Gartenimperator/SWH/resources/First_sketch.jpeg

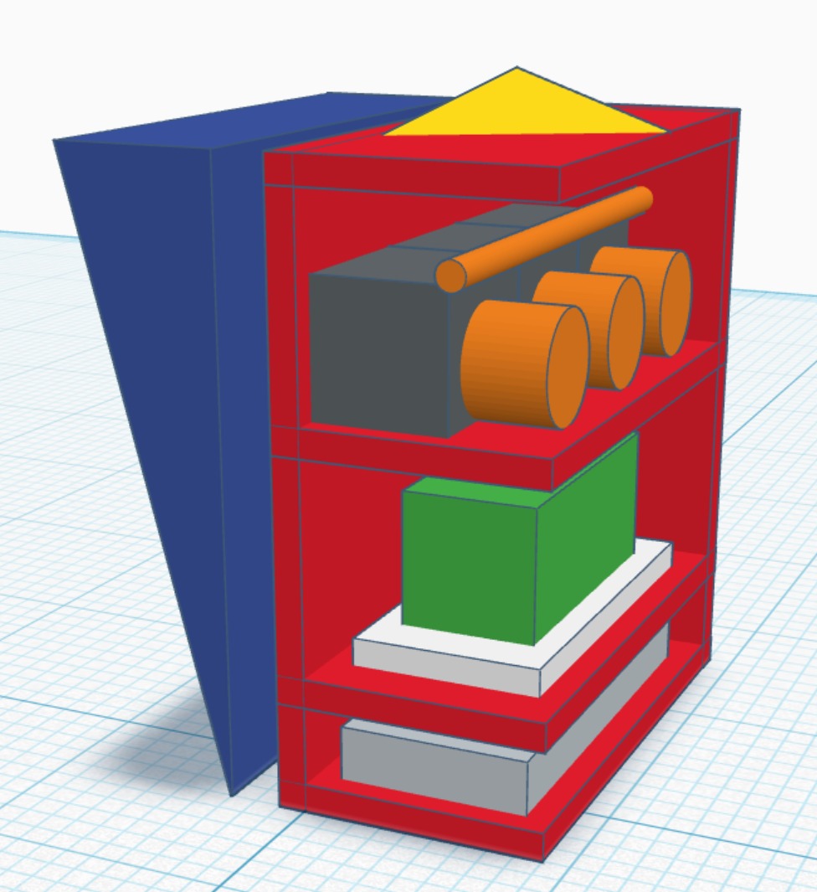
resources/First_sketch.jpeg
